GoblinDynamiteer/stepCounter/Dokumentation/Bilder/Foto/2017-04-18_back.jpeg

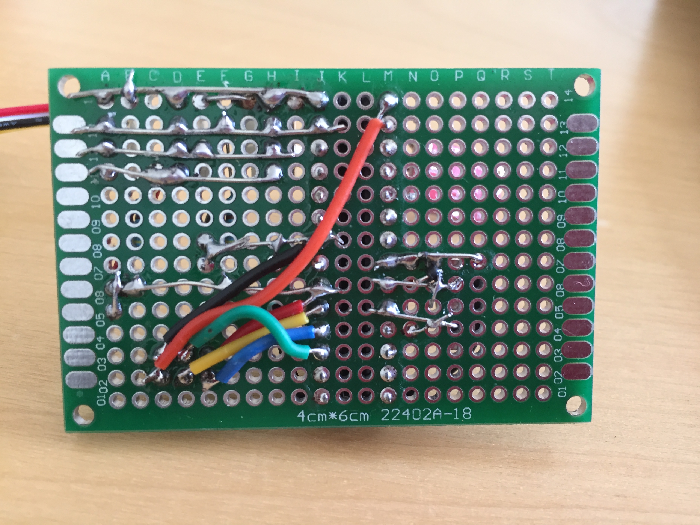
Dokumentation/Bilder/Foto/2017-04-18_back.jpeg
