GoblinDynamiteer/stepCounter/Dokumentation/Bilder/Foto/2017-04-18_front.jpeg

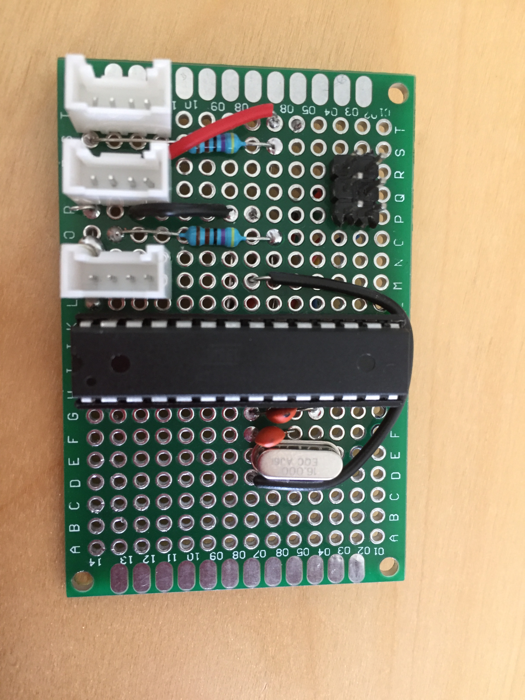
Dokumentation/Bilder/Foto/2017-04-18_front.jpeg
