GoblinDynamiteer/stepCounter/Dokumentation/Bilder/Foto/2017-04-19_final_pocketed.JPG

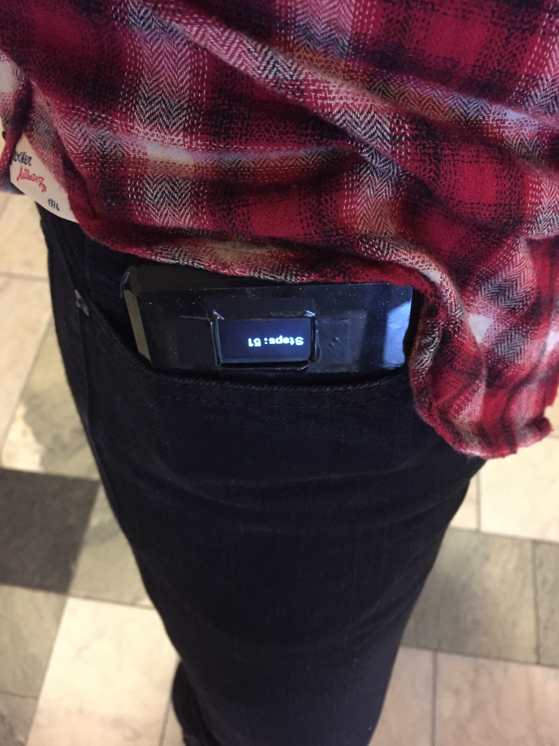
Dokumentation/Bilder/Foto/2017-04-19_final_pocketed.JPG
