GoblinDynamiteer/stepCounter/Dokumentation/Komponenter/Atmega 328p/Atmega328_pinout.png

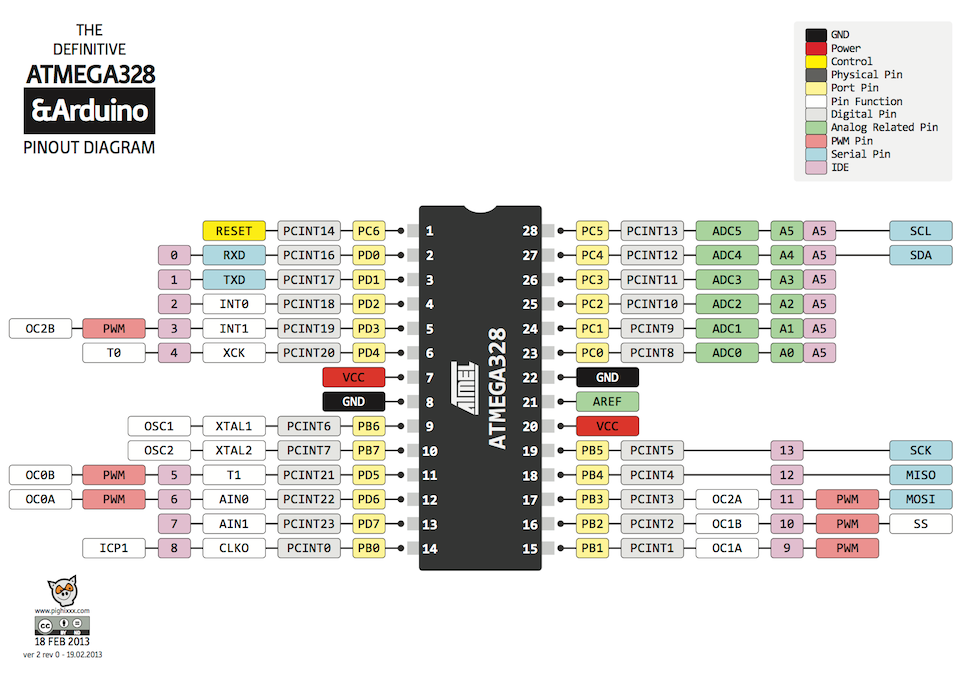
Dokumentation/Komponenter/Atmega 328p/Atmega328_pinout.png
