GoblinDynamiteer/stepCounter/Dokumentation/Komponenter/AVR Pocket Programmer/atmega_fuses_crystal160mHZ.PNG

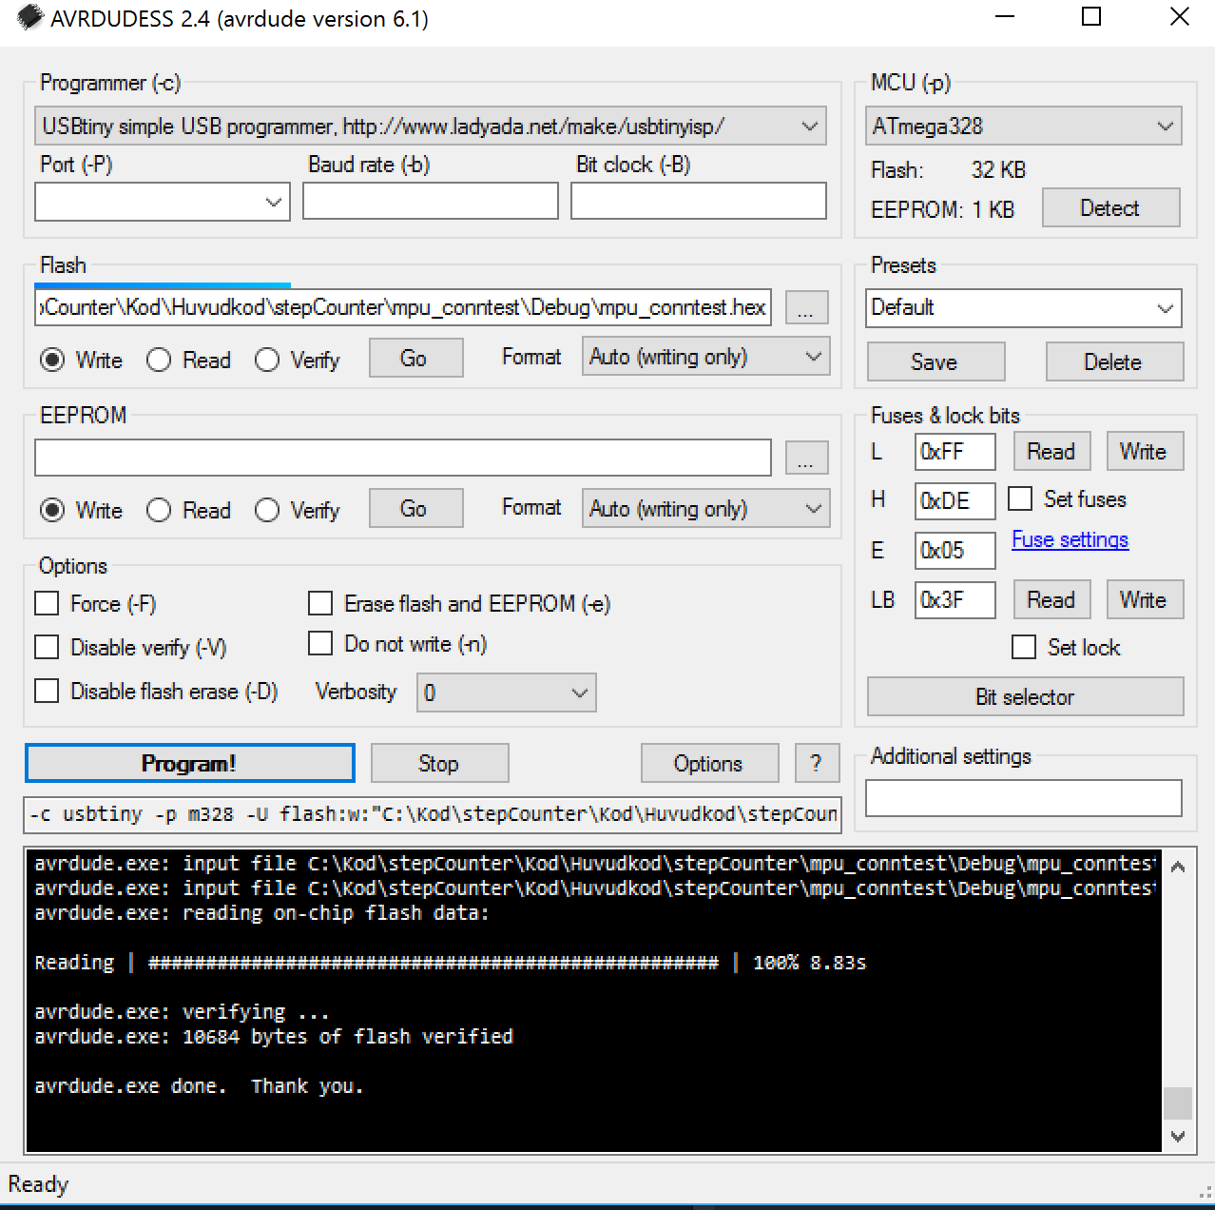
Dokumentation/Komponenter/AVR Pocket Programmer/atmega_fuses_crystal160mHZ.PNG
