GoblinDynamiteer/stepCounter/Dokumentation/Komponenter/AVR Pocket Programmer/connector_pinout.PNG

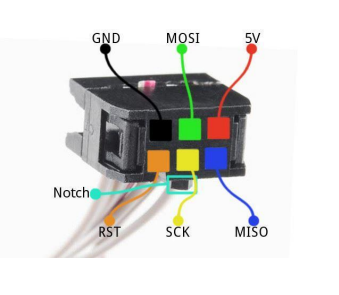
Dokumentation/Komponenter/AVR Pocket Programmer/connector_pinout.PNG
