GoblinDynamiteer/stepCounter/Dokumentation/Komponenter/Socket 24Pin/dimensions.jpg

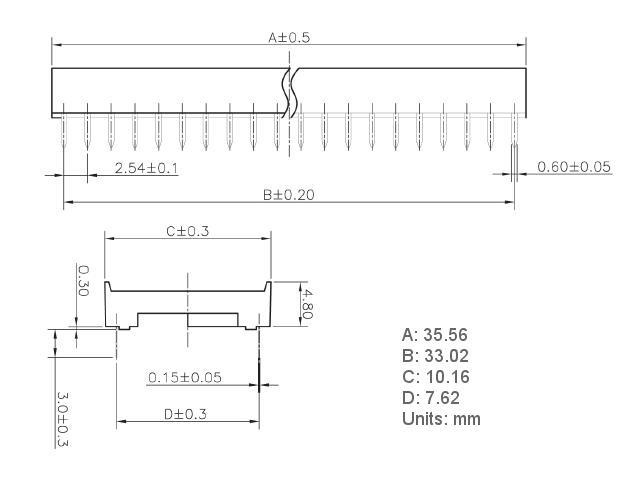
Dokumentation/Komponenter/Socket 24Pin/dimensions.jpg
