GoblinDynamiteer/stepCounter/Dokumentation/Kopplingsscheman/Fritzing/MPU_schem.png

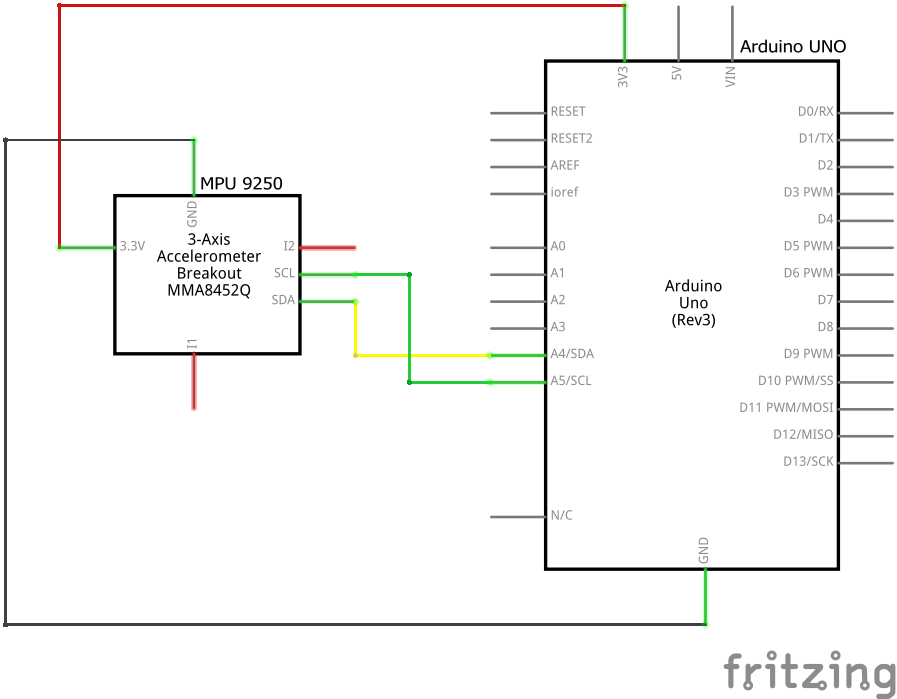
Dokumentation/Kopplingsscheman/Fritzing/MPU_schem.png
