GoblinDynamiteer/stepCounter/Dokumentation/Kopplingsscheman/Fritzing/Prototyp_1_schem.png

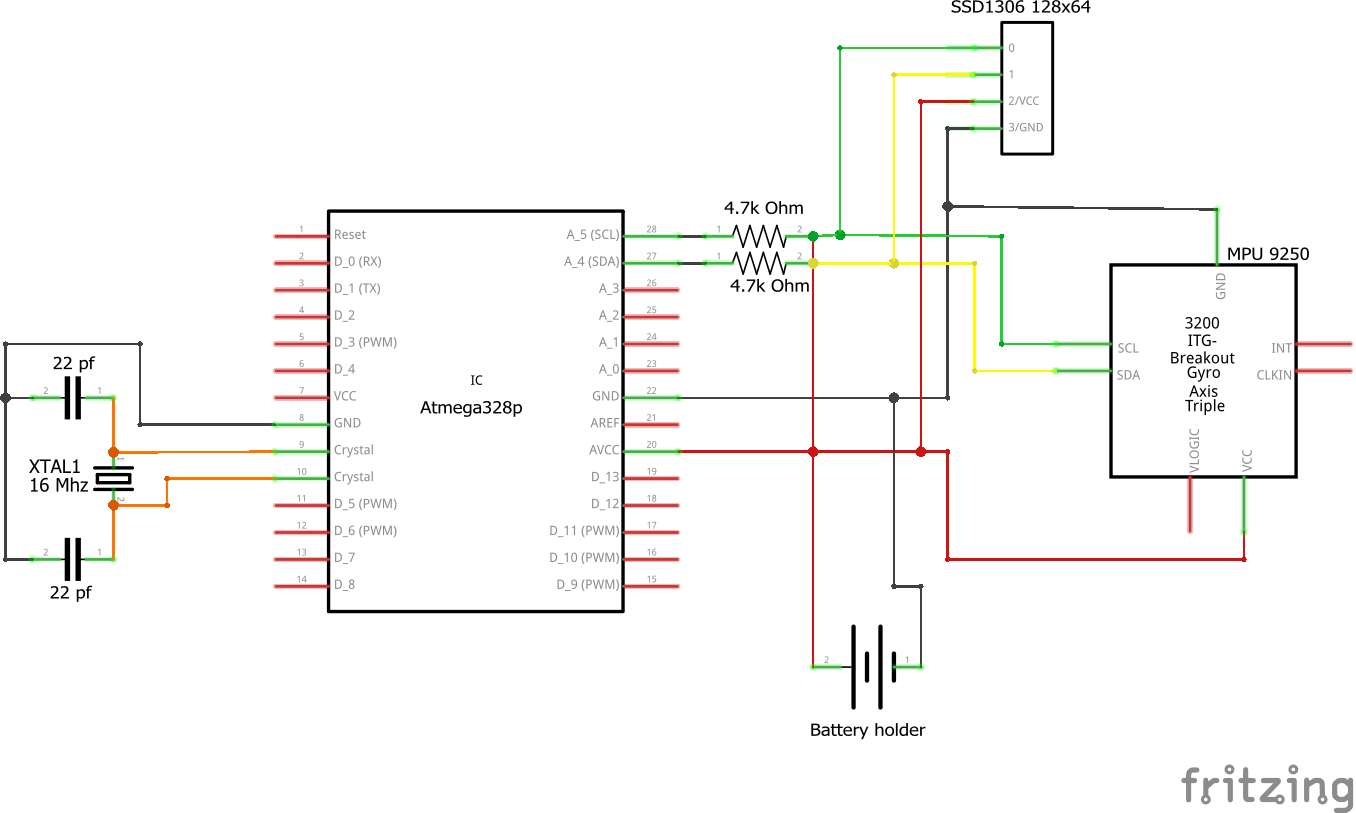
Dokumentation/Kopplingsscheman/Fritzing/Prototyp_1_schem.png
