GoblinDynamiteer/stepCounter/Dokumentation/Projekt/Report/images/proto2_hus1.png

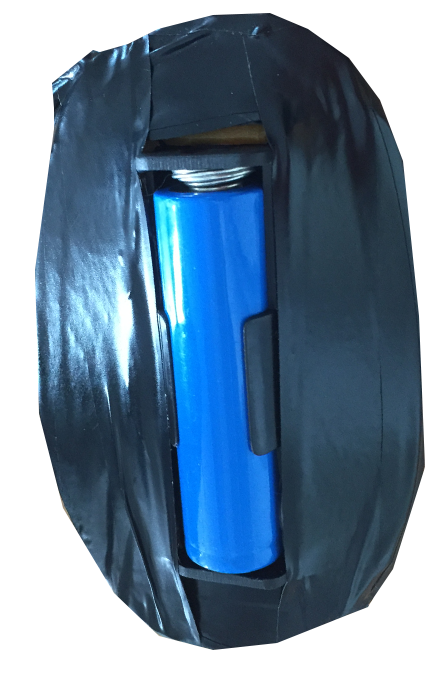
Dokumentation/Projekt/Report/images/proto2_hus1.png
