GoblinDynamiteer/stepCounter/Dokumentation/Projekt/PDF Export/stepCounter_rapport_3.pdf

# Stegräknare

Programmering av inbyggda system Mjukvaruutvecklare inbyggda system 2016

EJ FÄRDIG RAPPORT

Dennis Bunne
Simon Karlsson
Johan Kämpe

Stegräknare | 2017-04-10

# Sammanfattning

Skrivs när rapport är klar.

# Innehållsförteckning

Sammanfattning | 2
Innehållsförteckning | 3
1 Inledning | 4
1.1 Syfte | 4
1.2 Bakgrund | 4
1.2.1 Stegräknare | 4
1.2.2 I²C | 4
1.2.3 X-Y-Z | 4
2 Genomförande och resultat | 5
2.1 Använd programvara | 5
2.2 Komponentlista | 6
2.3 Utveckling av stegräknaren | 7
2.3.1 Prototyp 1 | 7
2.3.2 Prototyp 2 | 9
2.4 Stegräknarens funktion | 12
2.5 Kod | 13
2.5.1 Använda icke-standardbibliotek | 13
2.5.2 Globala variabler | 13
2.5.3 Definitioner / macron | 14
2.5.4 Funktioner | 14
3 Referenser | 15
4 Slutsats | 15

# 1 Inledning

## 1.1 Syfte

Syftet med projektet är att tillverka en bärbar, batteridriven stegräknare. Stegräknaren ska vara modulär, dvs det ska gå att ansluta och ta bort enheter, display, WiFi-modul m.m.

Initialt används en display för att visa antal steg. Stegen ska avläsas med hjälp av
en accelerometer, eller alternativt med en vibrations sensor.

Stegräknaren kan senare utökas med hastighetsmätare, tidräkning, ESP-modul eller bluetooth-modul för att skicka data m.m, om funktionen med stegräkning fungerar korrekt.

## 1.2 Bakgrund

### 1.2.1 Stegräknare

En stegräknare är en, vanligtvis portabel, enhet som mäter hur många steg en människa tar. Den kan användas vid exempelvis löpning eller promenad. Eller för att se hur många steg en person tar under en dag. Stegräknare kan också kallas pedometer.

### 1.2.2 I²C

I²C, Inter-Integrated Circuit, är ett sätt att koppla enheter till moderkort, inbyggda system, mobiltelefoner eller andra enheter. Kommunikation sker via två ledare, SDA (Serial Data Line, datasignal) och SCL (Serial Clock, klocksignal). Flera I²C-enheter kan anslutas till samma SDA-och SCL-ledare.

### 1.2.3 X-Y-Z

X, Y och Z används inom projektet för att beskriva riktningar i en tredimensionell miljö. MPU-9250-enheten har sensorer för acceleration i dessa tre riktningar. När enheten förs åt ett visst håll mäts rörelsens acceleration i denna riktning.

X- Y- och Z-riktningar.


# 2 Genomförande och resultat

## 2.1 Använd programvara

Vid utveckling av stegräknaren har följande programvara använts
Program | Beskrivning
Atmel Studio 7.0 | IDE för att skriva kod och kompilera till Atmel MCU.
Git | Versionshanteringsverktyg
GitKraken | Grafiskt gränssnitt för Git
Fritzing | Program för att skapa kretsscheman
Microsoft Word | Dokumentering
AVR Dudess | Program för att ladda upp koden till MCU i form av en HEX-fil.
Autodesk Fusion 360 | CAD-program för att skapa ett hölje för produkten

## 2.2 Komponentlista

För att bygga stegräknaren har följande hårdvara använts:

Artikel | Beskrivning
Atmel ATMega328-PU DIP-28N 8-bit MCU | Microprocessor.
SparkFun MPU-9250 | Enhet som mäter acceleration i X, Y och Z-riktning. Samt gyroskop, temperatur och kompass-funktionalitet.
Micro OLED Display SSD1306 128x64 | Display med upplösningen 128x64.
AVR pocket programmer | Enhet för att programmera Atmega-MCU
DIL-hållare 28-pin 0.3" | Sockel för Atmega-MCU
Resistor 4,7kΩ, 2 st | Pull up-resistorer för I²C-kanaler.
Kristalloscillator 16 MHz | Kopplas till MCU för att öka klockfrekvensen från 1 MHz till 16 MHz
Kondensator 22pF, 2 st | Ger jämn ström till Oscillatorn
Litiumbatteri 18650 | Strömförsörjning

Batterihållare för litiumbatteri 18650

Grovekontakter 4-stift | För modularisering av I²C-komponenter

## 2.3 Utveckling av stegräknaren

Två prototyper har byggts under projektets gång. Dessa beskrivs nedan.

### 2.3.1 Prototyp 1

Den första prototypen byggdes med en Arduino UNO och en breadboard dit komponenter kopplades. Prototypen testades genom att stoppa ner den i en ficka och promenerades runt med. Antal steg skrevs ut till Serial Monitor som finns i Arduinos IDE. En bärbar dator användes för strömförsörjning via USB, och för att se datan från Serial Monitor.

Både en accelerometer (MPU-9250) och vibrationssensor testades. Accelerometern valdes att gå vidare med, då denna ansågs ge bäst och stabilast värden.

Utskrift av steg till serial monitor:


Kopplingschema för prototyp 1:


### 2.3.2 Prototyp 2

Till prototyp nummer 2 används en Atmega328p MCU (Micro controller unit) i stället för Arduino. Komponenter har lötts samman på en platta och satts i ett hölje byggt av en optisk mus. Kontakter har använts för modularisering. Samtliga I2C-enheter går att byta ut eller placera om. Ett batteri används för strömförsörjning. Stegräknaren har minskat i storlek avsevärt sedan prototyp 1.

Fotografi på prototyp 2, utan hölje:

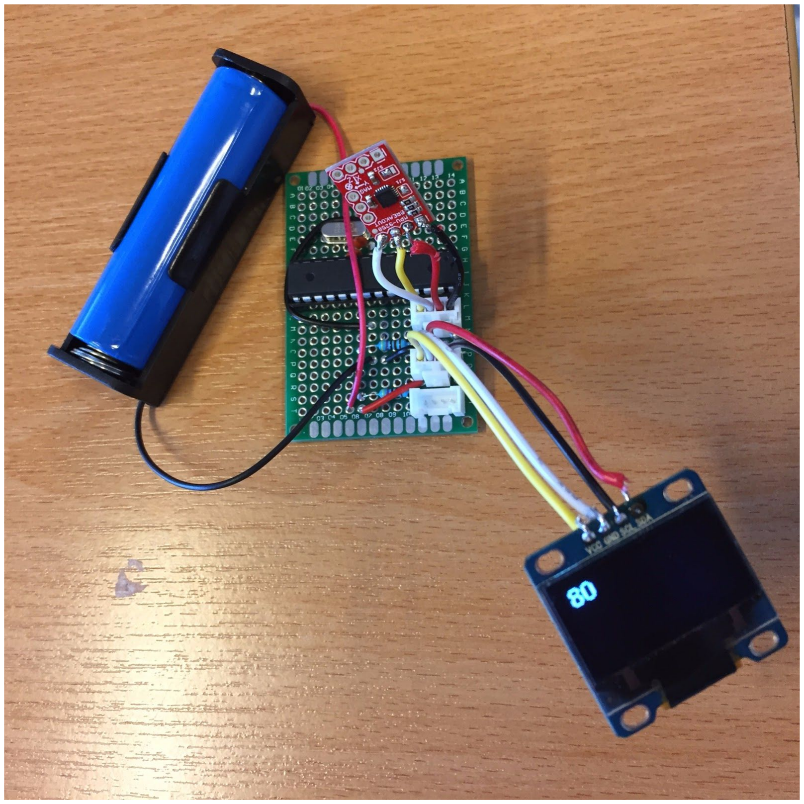
[picture p84: figure]

Fotografi på prototyp 2, med hölje:

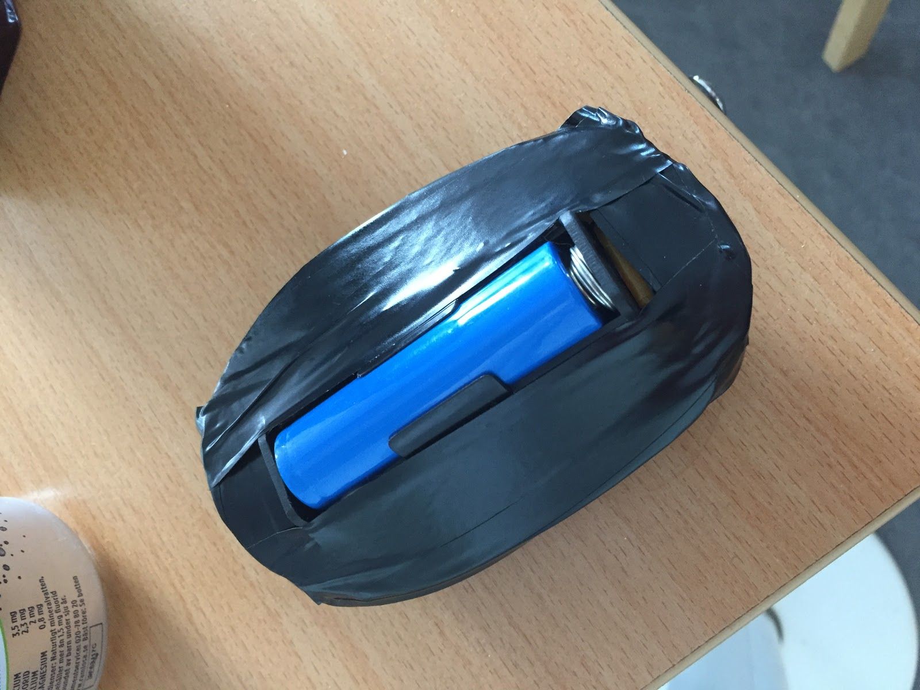
[picture p85: figure]

Kopplingschema för prototyp 2

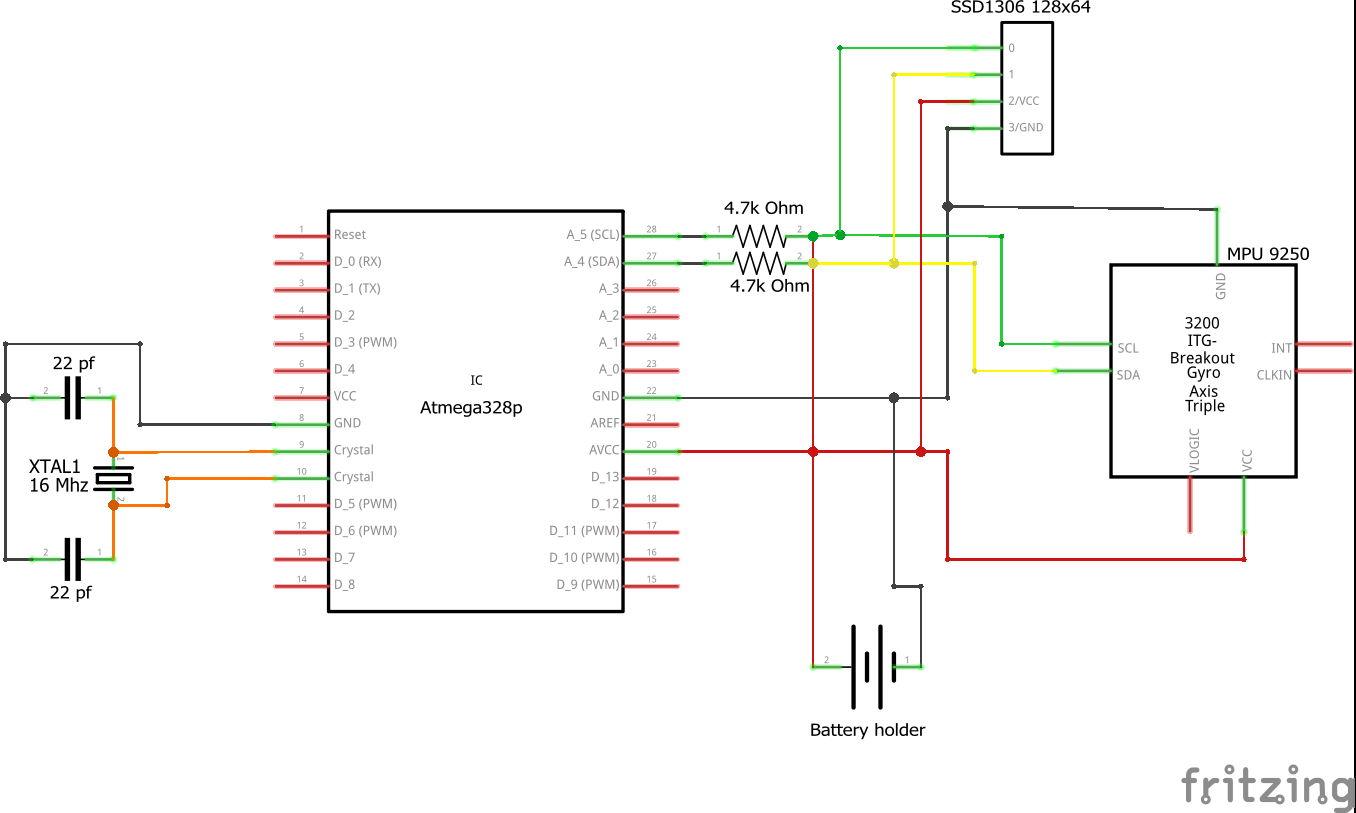
[picture p86: figure]

## 2.4 Stegräknarens funktion

Stegräknaren fungerar genom att hämta accelerationsdata från MPU-9250-enheten.

Värden för acceleration i riktningarna X, Y och Z adderas till ett enda värde. Detta sammansatta värde jämförs sedan mot ett värde som anses vara viloläge för accelerometern, dvs när den ligger helt stilla. Om skillnaden mellan dessa två värden överskrider ett visst satt tröskelvärde, så anses det att ett steg har tagits.

Vid varje taget steg uppdateras stegräknarens display med totalt antal tagna steg.

## 2.5 Kod

Koden för stegräknaren är skrivet i programspråket C. Redan färdiga kodbibliotek för displayen, accelerometern och I2C har använts för att underlätta programmeringsarbetet.

Utförligare kommentering av koden finns i källkodsfilen.

### 2.5.1 Använda icke-standardbibliotek

Namn | Författare | Beskrivning
I2C master library using hardware TWI interface | Peter Fleury | I2C-funktionalitet för AVR-enheter (Atmel MCUer)
MPU6050 lib 0x02 | Davide Gironi | För accelerometer-enheten, via I2C.
Universal 8bit Graphics Library | olikraus@gmail.com | För display, via I2C.

### 2.5.2 Globala variabler

Följande globala variabler används i projektets kod.
Namn | Beskrivning
uint16_t steps | Håller antal steg
double accIdle | Värde som sätts vid programmets uppstart, håller det värde som accelerometern ger när den ligger helt stilla.
double accCombined | Sammansatt accelerationsvärde från X- Y- och Z-riktning.
double accX, accY, accZ | Värden för acceleration i X- Y- och Z-riktning.

### 2.5.3 Definitioner / macron

Följande macron används i projektets kod
Namn | Värde | Beskrivning
X | 0x3B | Address för accelerometerdata i X-riktning i MPU
Y | 0x3D | Address för accelerometerdata i Y-riktning i MPU
Z | 0x3F | Address för accelerometerdata i Z-riktning i MPU
STEP_ACC_TRIGGER | 2.3 | Tröskelvärde för att bestämma om ett steg har tagits.

### 2.5.4 Funktioner

Beskrivning av egenskrivna funktioner i projektets kod

Namn | Beskrivning
double getAcc(int addr); | Hämtar accelerationsdata från MPU och ger värdet i retur, angivet som g-kraft (SANT????). Som argument tar funktionen adressen till det register som ska läsas. Dessa adresser är definierade som macron X, Y och Z.
void drawSteps(uint16_t steps); | Skriver ut aktuellt antal steg till displayen.
void drawString(char * string); | Skriver ut en text till displayen. Texten ges som argument till funktionen, i form av en pekare till en char-sträng.
void setAccIdle(); | Sätter ett värde till den globala variabeln accIdle. Funktionen körs endast en gång vid varje uppstart av programmet.
double getAccXYZ(void); | Använder sig av funktionen getAcc för att hämta accelerationsdata från X-, Y- och Z-riktningen. Det adderade värdet ges i retur.

# 3 Referenser

Länkar till författare av kodbibliotek MPU 6050 library - Davide Gironi (http://davidegironi.blogspot.se/2013/02/avr-atmega-mpu6050-gyroscope-and.html#.WOtTeojyhPY)
U8glib - Olikarus (https://github.com/olikraus)
I2C master library - Peter Fleury (http://homepage.hispeed.ch/peterfleury)

Länkar till använda datablad för komponenter MPU9250 (https://cdn.sparkfun.com/assets/learn_tutorials/5/5/0/MPU9250REV1.0.pdf)
Atmega328p (http://www.atmel.com/Images/Atmel-42735-8-bit-AVR-Microcontroller-ATmega328-328P_Datasheet.pdf)
SSD1306 Oled Display 128x64 (https://github.com/GoblinDynamiteer/stepCounter/blob/master/Dokumentation/Komponenter/Micro%20OLED%20Breakout%20Display%20SSD1306/SSD1306_datasheet.pdf)

# 4 Slutsats

Skrivs senare
