GoblinDynamiteer/stepCounter/CAD/Inventor Project/renders/stepCounterHousing2.png

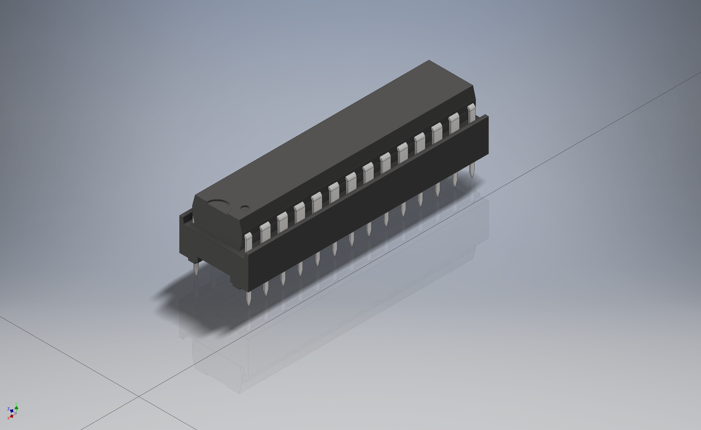
CAD/Inventor Project/renders/stepCounterHousing2.png
