GoblinDynamiteer/stepCounter/CAD/Inventor Project/renders/stepCounterHousing.png

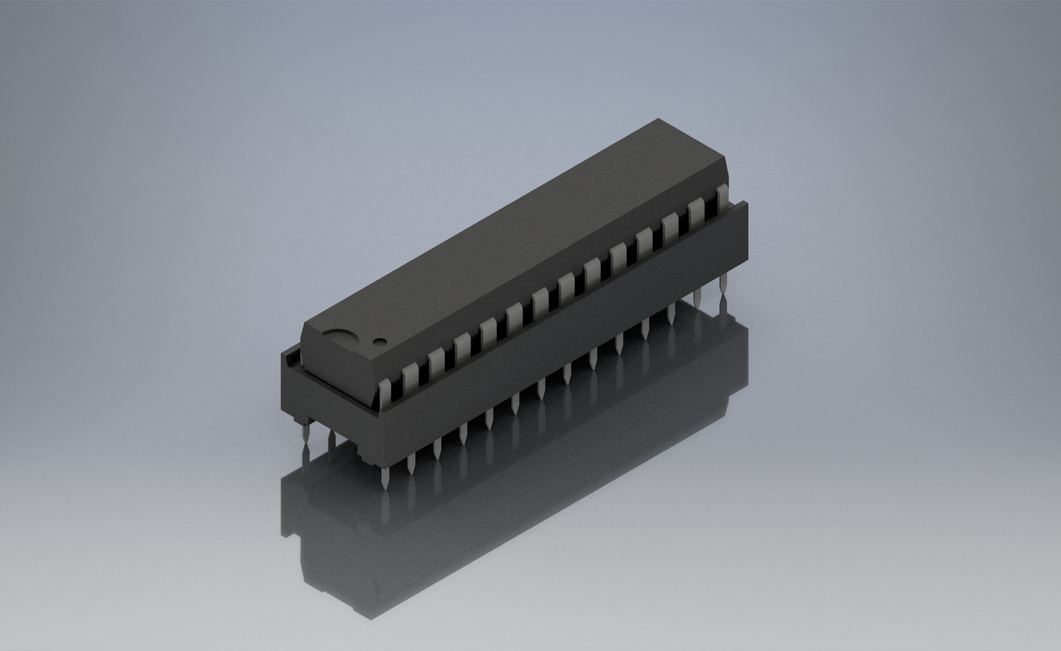
CAD/Inventor Project/renders/stepCounterHousing.png
