GoblinDynamiteer/stepCounter/Dokumentation/Bilder/Foto/2017-04-19_final_assembly.JPG

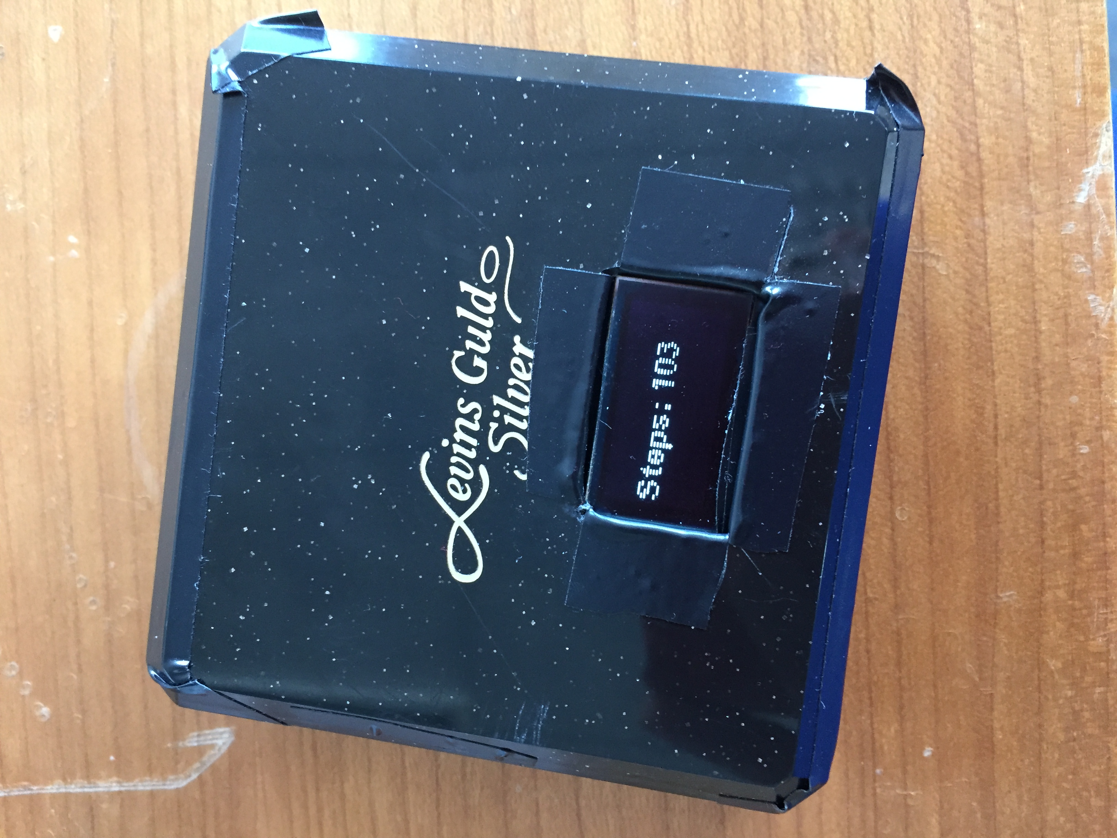
Dokumentation/Bilder/Foto/2017-04-19_final_assembly.JPG
