GoblinDynamiteer/stepCounter/Dokumentation/Bilder/Foto/measurements/base_h.jpg

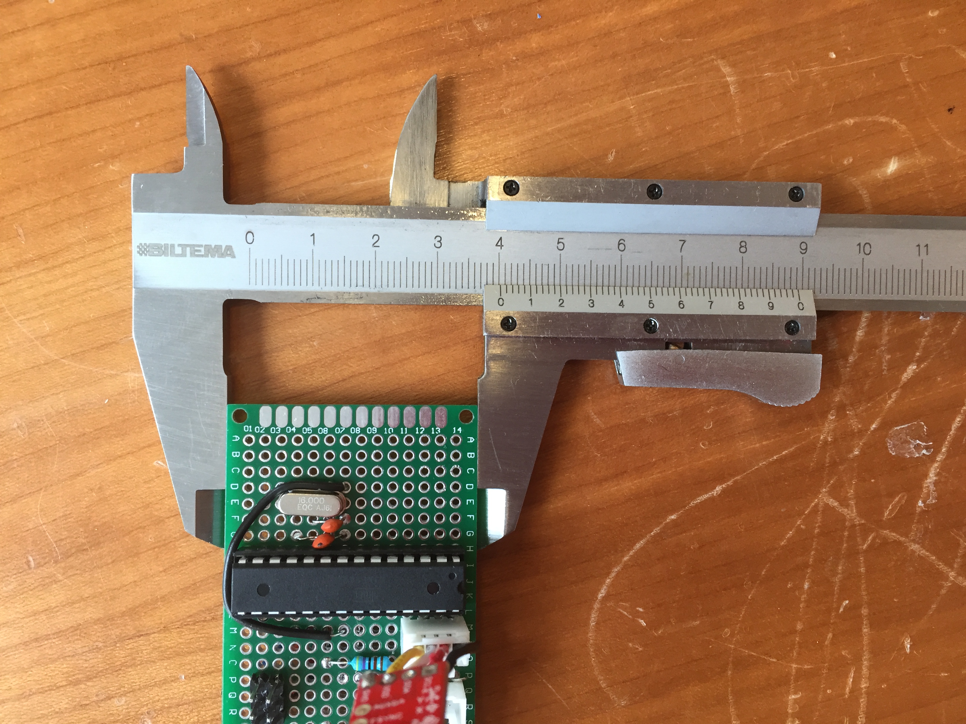
Dokumentation/Bilder/Foto/measurements/base_h.jpg
