GoblinDynamiteer/stepCounter/Dokumentation/Bilder/Foto/measurements/base_t.jpg

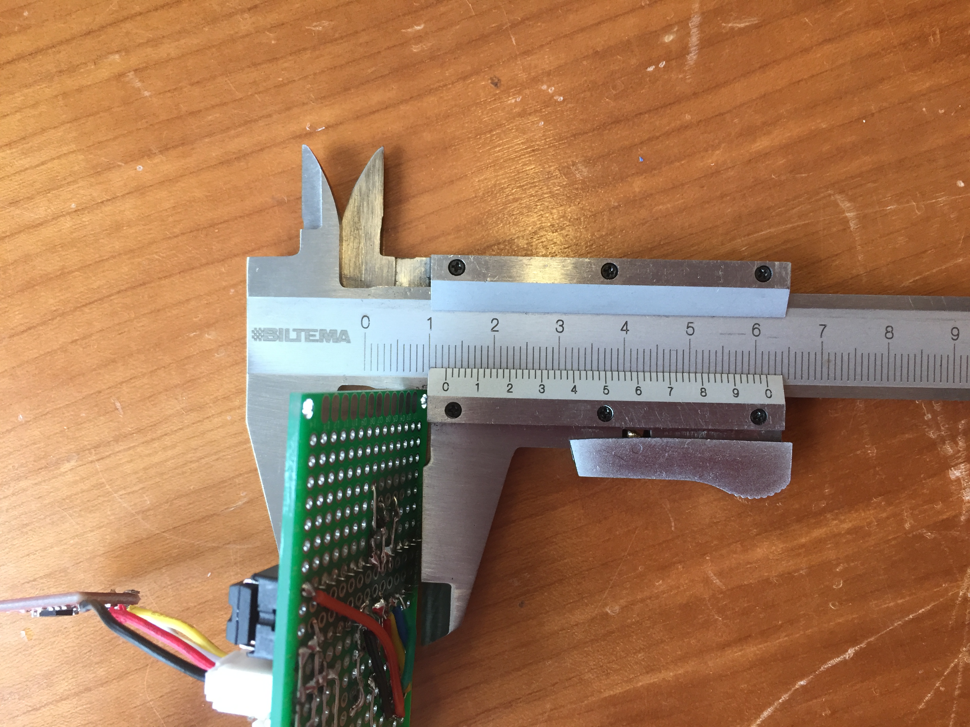
Dokumentation/Bilder/Foto/measurements/base_t.jpg
