GoblinDynamiteer/stepCounter/Dokumentation/Bilder/Foto/measurements/base_w.jpg

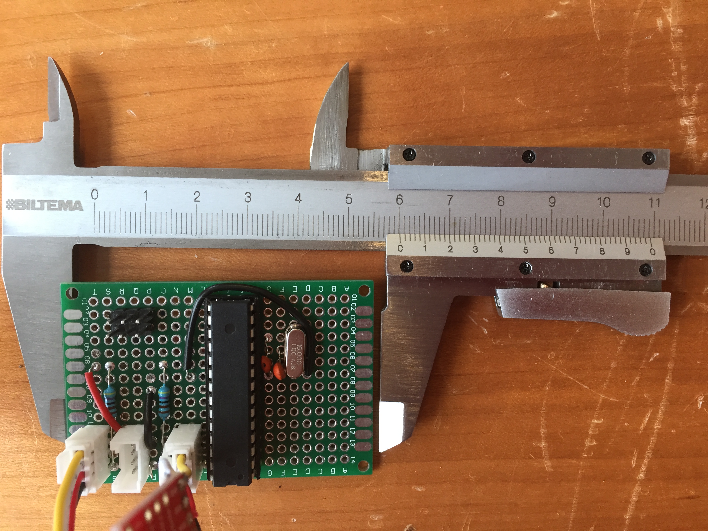
Dokumentation/Bilder/Foto/measurements/base_w.jpg
