GoblinDynamiteer/stepCounter/Dokumentation/Bilder/Foto/measurements/disp_h.jpg

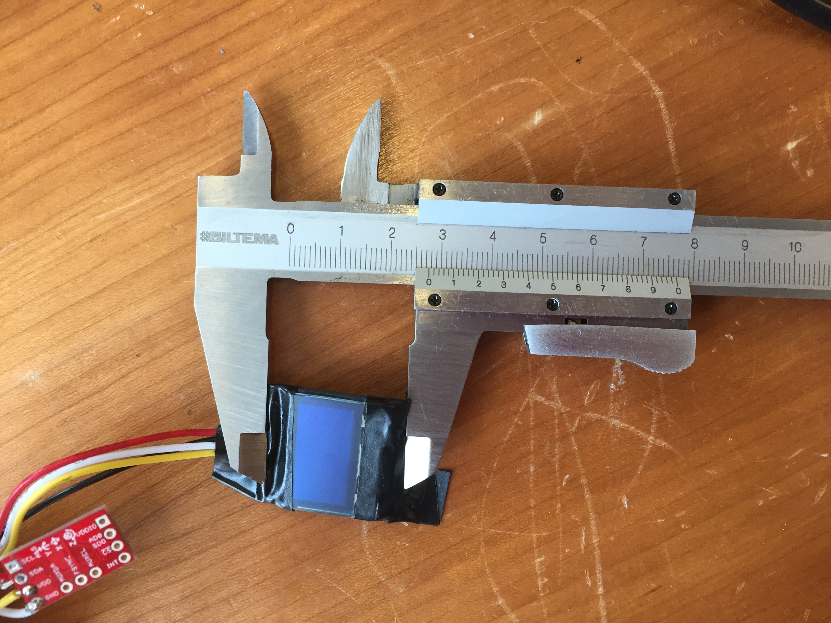
Dokumentation/Bilder/Foto/measurements/disp_h.jpg
