GoblinDynamiteer/stepCounter/Dokumentation/Bilder/Foto/measurements/disp_w.jpg

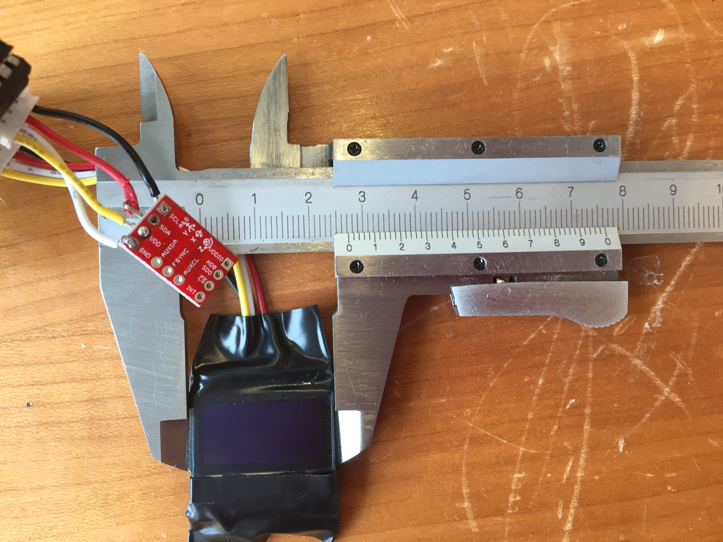
Dokumentation/Bilder/Foto/measurements/disp_w.jpg
