GoblinDynamiteer/stepCounter/Dokumentation/Bilder/Foto/measurements/mpu_h.jpg

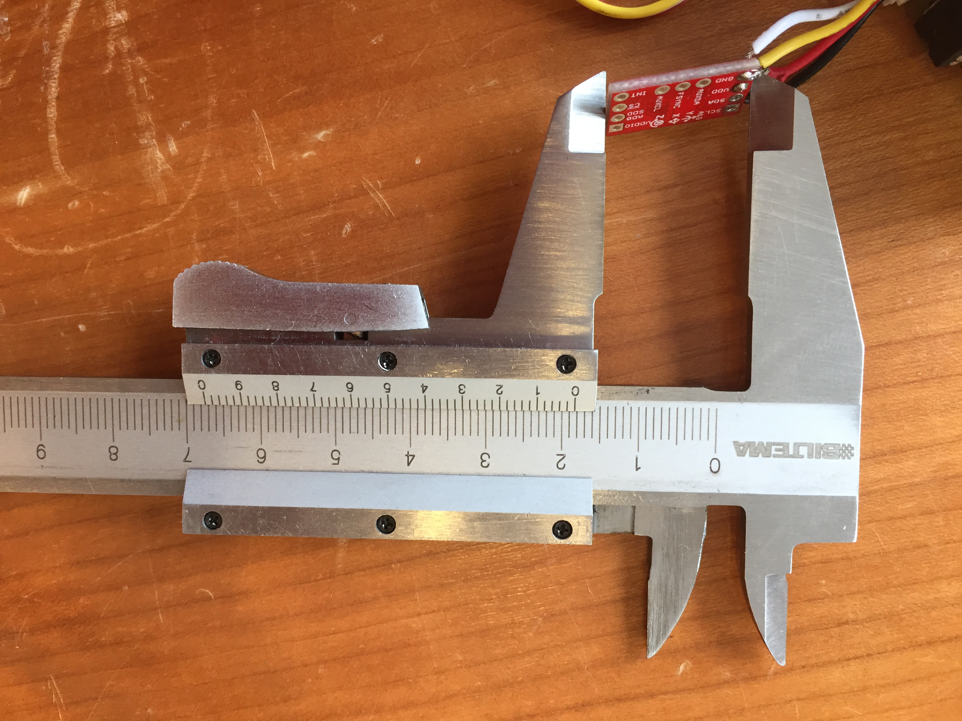
Dokumentation/Bilder/Foto/measurements/mpu_h.jpg
