GoblinDynamiteer/stepCounter/Dokumentation/Bilder/Foto/measurements/mpu_w.jpg

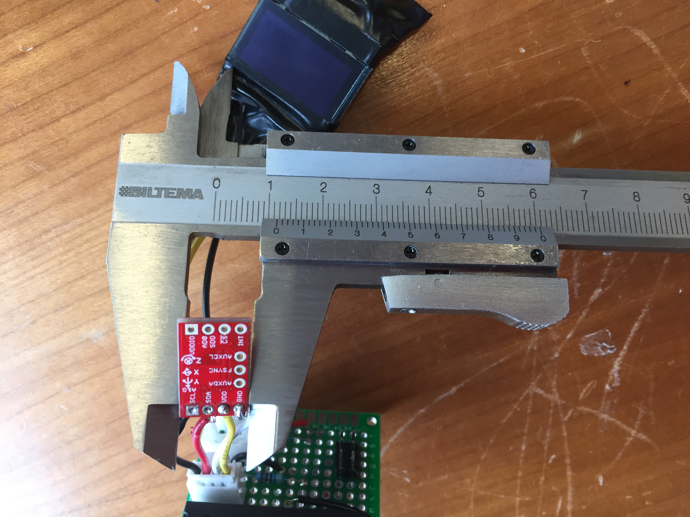
Dokumentation/Bilder/Foto/measurements/mpu_w.jpg
