GoblinDynamiteer/stepCounter/Dokumentation/Komponenter/Atmega 328p/ATmega328P_dimensions.pdf

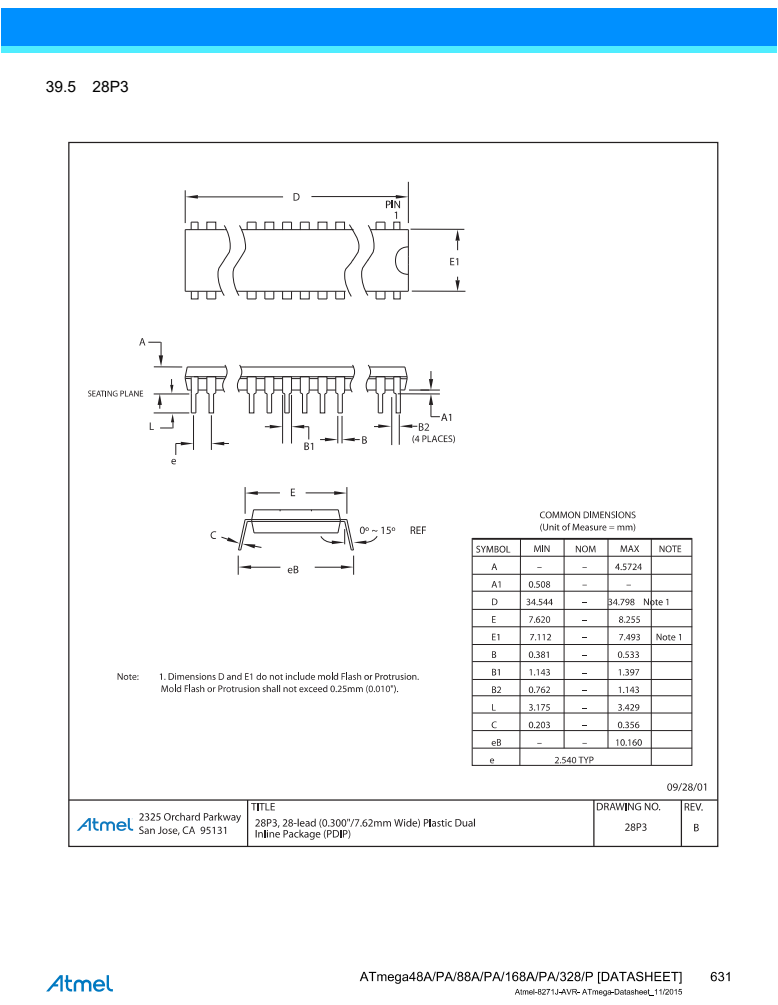
[picture p97: page 1]
