GoblinDynamiteer/stepCounter/Kod/Testkod/AVR/OLEDLib/OLEDLib/myFont.c

unsigned char Ascii_1[97][5]={     // Refer to "Times New Roman" Font Database...
                                   //   Basic Characters
    {0xFF,0xFF,0xFF,0xFF,0xFF},     //   (  0)    - 0x0000 Empty set
    {0x00,0x00,0x4F,0x00,0x00},     //   (  1)  ! - 0x0021 Exclamation Mark
    {0x00,0x07,0x00,0x07,0x00},     //   (  2)  " - 0x0022 Quotation Mark
    {0x14,0x7F,0x14,0x7F,0x14},     //   (  3)  # - 0x0023 Number Sign
    {0x24,0x2A,0x7F,0x2A,0x12},     //   (  4)  $ - 0x0024 Dollar Sign
    {0x23,0x13,0x08,0x64,0x62},     //   (  5)  % - 0x0025 Percent Sign
    {0x36,0x49,0x55,0x22,0x50},     //   (  6)  & - 0x0026 Ampersand
    {0x00,0x05,0x03,0x00,0x00},     //   (  7)  ' - 0x0027 Apostrophe
    {0x00,0x1C,0x22,0x41,0x00},     //   (  8)  ( - 0x0028 Left Parenthesis
    {0x00,0x41,0x22,0x1C,0x00},     //   (  9)  ) - 0x0029 Right Parenthesis
    {0x14,0x08,0x3E,0x08,0x14},     //   ( 10)  * - 0x002A Asterisk
    {0x08,0x08,0x3E,0x08,0x08},     //   ( 11)  + - 0x002B Plus Sign
    {0x00,0x50,0x30,0x00,0x00},     //   ( 12)  , - 0x002C Comma
    {0x08,0x08,0x08,0x08,0x08},     //   ( 13)  - - 0x002D Hyphen-Minus
    {0x00,0x60,0x60,0x00,0x00},     //   ( 14)  . - 0x002E Full Stop
    {0x20,0x10,0x08,0x04,0x02},     //   ( 15)  / - 0x002F Solidus
    {0x3E,0x51,0x49,0x45,0x3E},     //   ( 16)  0 - 0x0030 Digit Zero
    {0x00,0x42,0x7F,0x40,0x00},     //   ( 17)  1 - 0x0031 Digit One
    {0x42,0x61,0x51,0x49,0x46},     //   ( 18)  2 - 0x0032 Digit Two
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
    {0x02,0x01,0x02,0x04,0x02},     //   ( 94)  ~ - 0x007E Tilde
    {0x08,0x0C,0x0E,0x0C,0x08},     //   ( 95)  upward facing triangle/arrow
    {0x08,0x18,0x38,0x18,0x08},     //   ( 96)  downward facing triangle/arrow
};
